justDevelo-ping/Vectrex/reference/3d model/Coolate/VectrexControllerJoystickWithNotch.stl

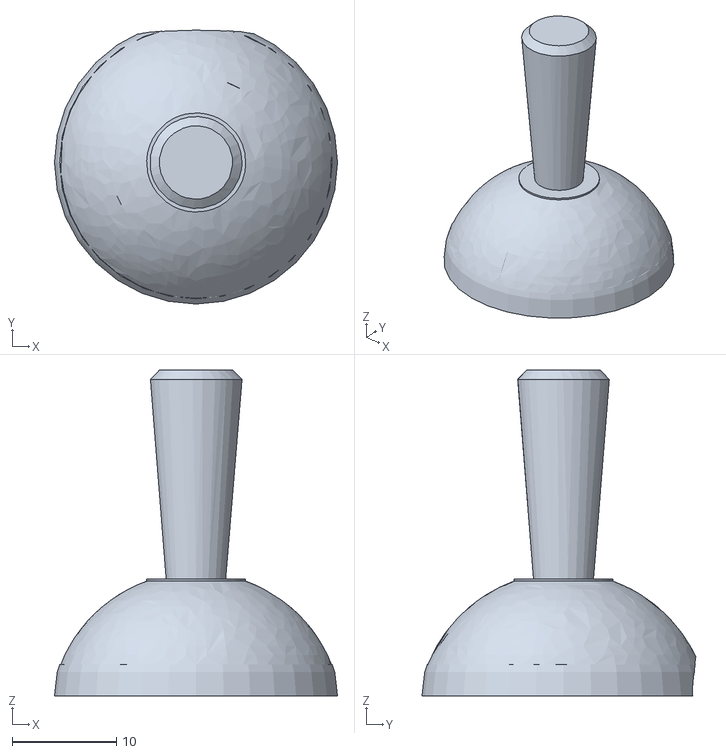
[picture p17: CAD file, 2024-08-31]
reference/3d model/Coolate/VectrexControllerJoystickWithNotch.stl
27.1 x 26.2 x 31.2
